olewolf/geophone/twiddle_factors_256_br.h

/* 256 bit-reversed twiddle factors scaled to an amplitude of 0.5. */

#ifndef _TWIDDLE_FACTORS_256_BR
#define _TWIDDLE_FACTORS_256_BR


#define __PROG_TYPES_COMPAT__
#include <avr/pgmspace.h>

const int16_t twiddle_real[ 256 ] PROGMEM =
{
  0x7fff, 0x0000, 0x5a82, 0xa57e, 0x7641, 0xcf05, 0x30fb, 0x89bf, 
  0x7d8a, 0xe708, 0x471c, 0x9593, 0x6a6d, 0xb8e4, 0x18f8, 0x8276, 
  0x7f62, 0xf375, 0x5133, 0x9d0e, 0x70e2, 0xc3aa, 0x2528, 0x8583, 
  0x7a7d, 0xdad8, 0x3c56, 0x8f1e, 0x62f2, 0xaecd, 0x0c8b, 0x809e, 
  0x7fd8, 0xf9b9, 0x55f5, 0xa129, 0x73b5, 0xc946, 0x2b1f, 0x877c, 
  0x7c29, 0xe0e7, 0x41ce, 0x9236, 0x66cf, 0xb3c1, 0x12c8, 0x8163, 
  0x7e9d, 0xed38, 0x4c3f, 0x9931, 0x6dca, 0xbe32, 0x1f19, 0x83d7, 
  0x7884, 0xd4e1, 0x36ba, 0x8c4b, 0x5ed7, 0xaa0b, 0x0647, 0x8028, 
  0x7ff6, 0xfcdc, 0x5842, 0xa34c, 0x7504, 0xcc22, 0x2e11, 0x8894, 
  0x7ce3, 0xe3f5, 0x447a, 0x93dc, 0x68a6, 0xb64c, 0x15e2, 0x81e3, 
  0x7f09, 0xf055, 0x4ebf, 0x9b18, 0x6f5f, 0xc0e9, 0x2223, 0x84a3, 
  0x798a, 0xd7da, 0x398c, 0x8dab, 0x60ec, 0xac65, 0x096a, 0x8059, 
  0x7fa7, 0xf696, 0x539b, 0x9f14, 0x7255, 0xc674, 0x2826, 0x8676, 
  0x7b5d, 0xdddd, 0x3f17, 0x90a1, 0x64e8, 0xb141, 0x0fab, 0x80f7, 
  0x7e1d, 0xea1e, 0x49b4, 0x975a, 0x6c24, 0xbb86, 0x1c0b, 0x831d, 
  0x776c, 0xd1ef, 0x33de, 0x8afc, 0x5cb4, 0xa7be, 0x0324, 0x800a, 
  0x7ffd, 0xfe6e, 0x5964, 0xa463, 0x75a5, 0xcd92, 0x2f87, 0x8927, 
  0x7d39, 0xe57e, 0x45cd, 0x94b6, 0x698c, 0xb797, 0x176d, 0x822a, 
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
  0xdc5a, 0x8511, 0x8fdd, 0xc248, 0xb005, 0x9c11, 0x80c8, 0xf1e5, 
  0xe893, 0x822a, 0x9674, 0xb797, 0xba33, 0x94b6, 0x82c7, 0xe57e, 
  0xd079, 0x8927, 0x8a5b, 0xcd92, 0xa69c, 0xa463, 0x8003, 0xfe6e
};

#endif /* _TWIDDLE_FACTORS_256_BR */
